vidurawarna/voice_recorder_EN1093_Project_G15/Simulations/Proteus/Sound_output/Speaker/Speaker.ino

void setup() {
  //Serial.begin(9600);
  for ( int i=0; i<8; i++){
    pinMode(i, OUTPUT);
  }
}

void loop() {
  /*for (int t=0; t<100; t++){
    PORTD = sine[t];
    delay(10);*/
    int t = analogRead(A0);
    PORTD = t;
    delayMicroseconds(8);
    PORTD = analogRead(A0);
    delayMicroseconds(1);
}
